jbazant/esp8266-binary-clock/esp8266-binary-clock/ClockDisplay.h

#ifndef ClockDisplay_h
#define ClockDisplay_h

#include <Arduino.h>
#include "LedController.hpp"
#include "MyDHT.h"
#include "MyNTPClient.h"
#include "WithTicker.h"
#include <moonPhase.h>

#define DEFAULT_INTENSITY 0
#define INTENSITY_STEP 7

class ClockDisplay: public WithTicker {
  public:
    ClockDisplay(const uint8_t dinPin, const uint8_t clkPin, const uint8_t csPin, MyDHT* dhtSensor, MyNTPClient* ntpClient, const uint refreshRate);

    void changeIntensity();
    void switchSegment();
    void renderLoading();

  protected:
    void onTick();

  private:
    LedController<1, 1> lc_;
    MyDHT* dhtSensor_;
    MyNTPClient* ntpClient_;
    moonPhase moonPhase_;

    uint8_t currentIntensity_;
    bool isSegmentOn_;

    uint dowShifted_();
    void renderClockRows_();
    void renderDHTRows_();
    void render_();

    uint8_t getDHTFlags_();
    uint8_t getNTPFlags_();
    uint8_t getMoonPhase_();
};

#endif
